KeesvdBerg/TDM-Test-Setup/Solidworks model of prototype/Motor mounting plate.SLDPRT

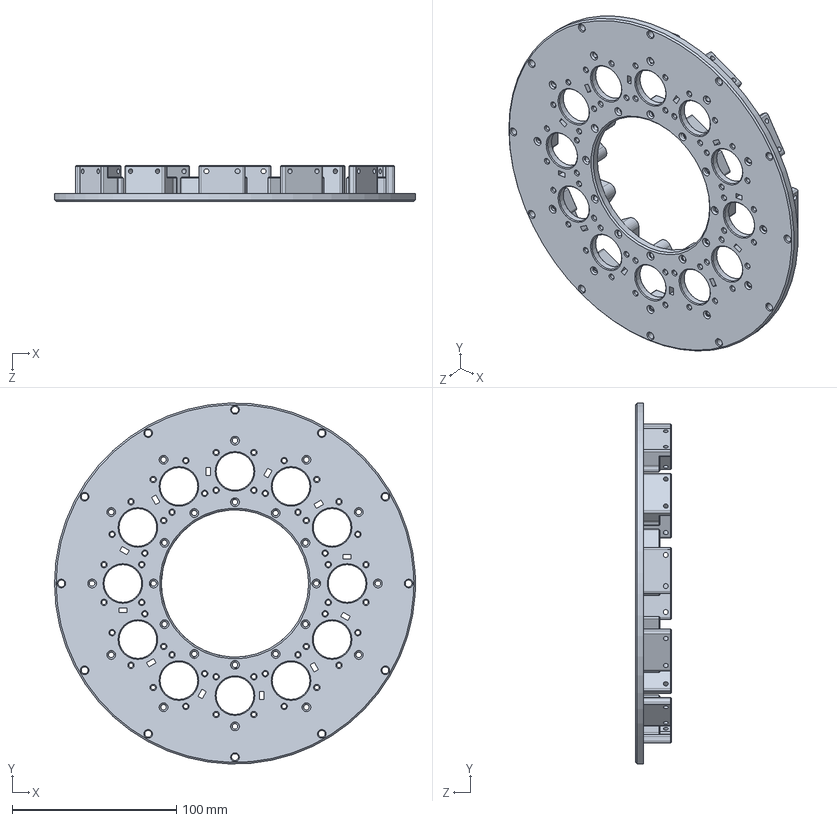
[picture p15: CAD file, 2024-05-05]
Solidworks model of prototype/Motor mounting plate.SLDPRT
220.0 x 219.9 x 22.0 mm
