KeesvdBerg/TDM-Test-Setup/Solidworks model of prototype/Magnet 5mm-5mm.SLDPRT

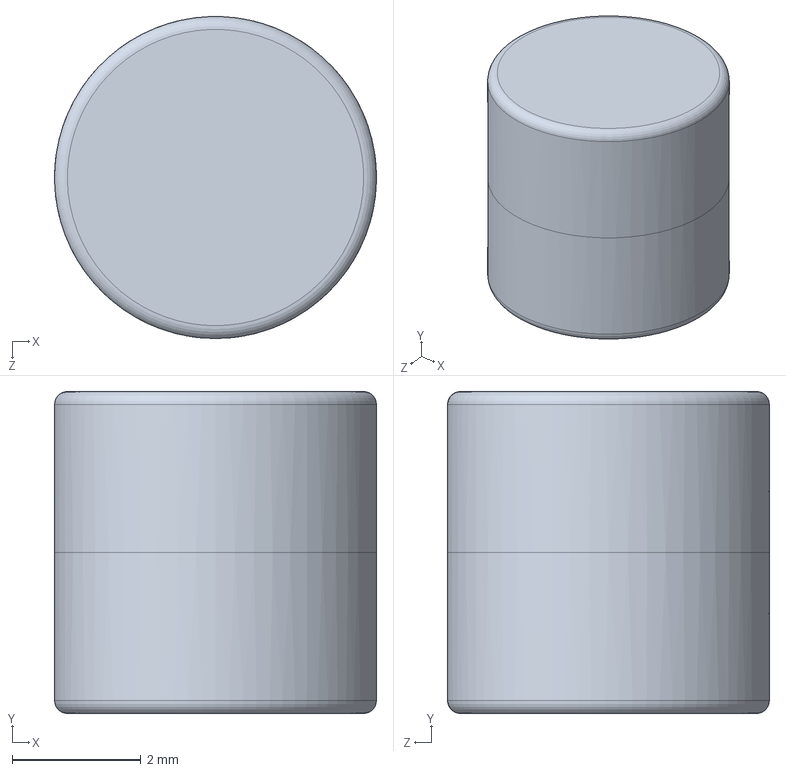
[picture p16: CAD file, 2024-05-05]
Solidworks model of prototype/Magnet 5mm-5mm.SLDPRT
5.00 x 5.00 x 5.00 mm
