KeesvdBerg/TDM-Test-Setup/Solidworks model of prototype/Heat set insert.SLDPRT

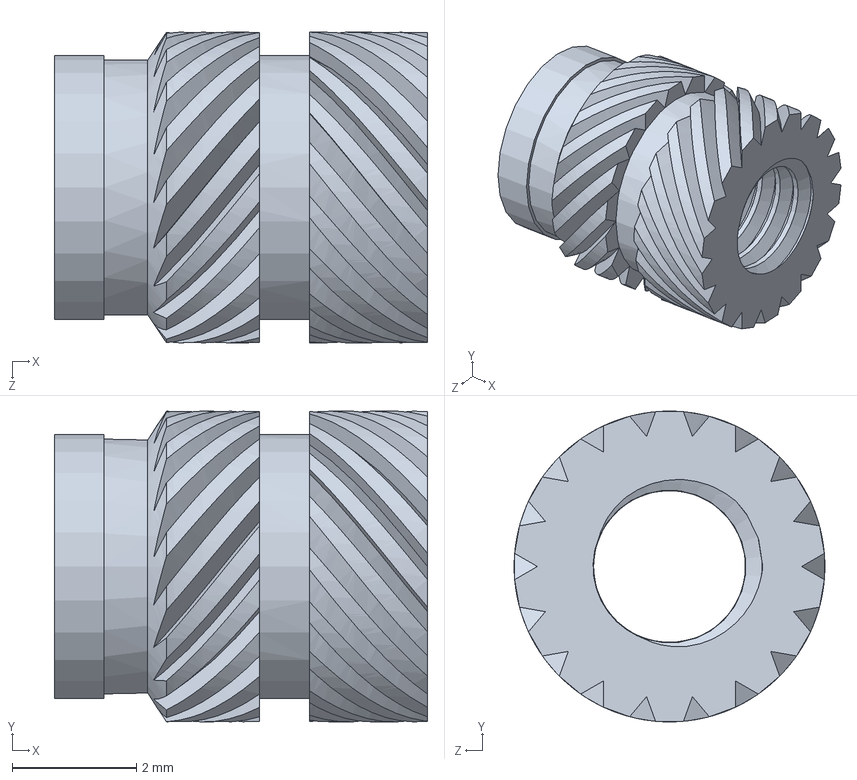
[picture p17: CAD file, 2024-05-05]
Solidworks model of prototype/Heat set insert.SLDPRT
6.00 x 5.00 x 5.00 mm
