KeesvdBerg/TDM-Test-Setup/Solidworks model of prototype/MTI lock mounting plate.SLDPRT

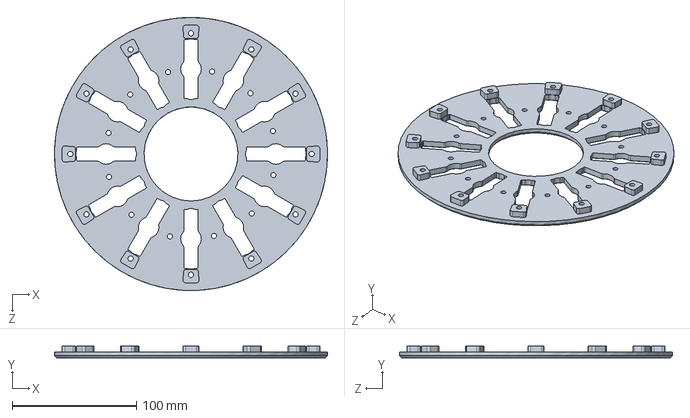
[picture p18: CAD file, 2024-05-05]
Solidworks model of prototype/MTI lock mounting plate.SLDPRT
219.9 x 10.0 x 220.0 mm
