KeesvdBerg/TDM-Test-Setup/Solidworks model of prototype/Acme thread.SLDPRT

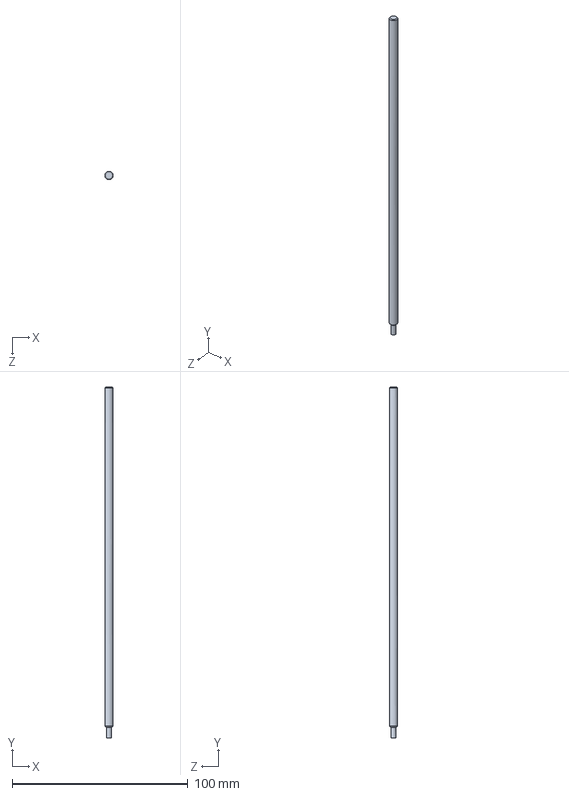
[picture p19: CAD file, 2024-05-05]
Solidworks model of prototype/Acme thread.SLDPRT
4.75 x 200.0 x 4.76 mm
