KeesvdBerg/TDM-Test-Setup/Solidworks model of prototype/Distal connector ring.SLDPRT

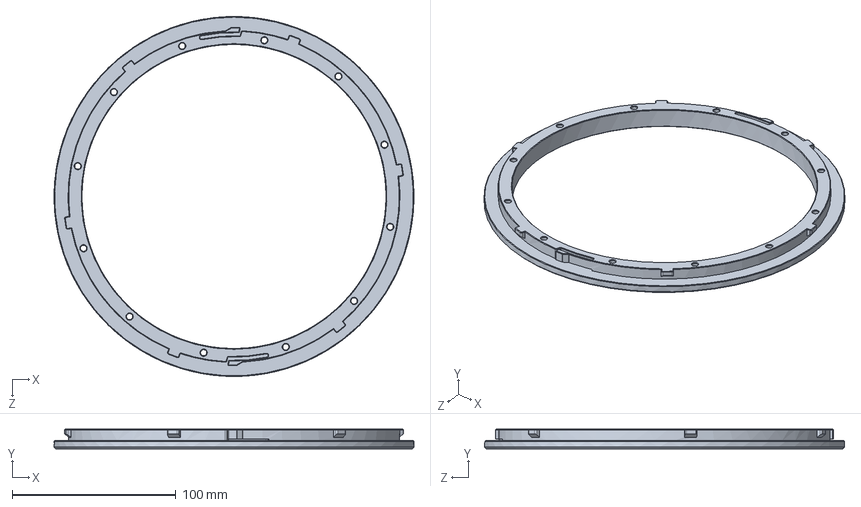
[picture p20: CAD file, 2024-05-05]
Solidworks model of prototype/Distal connector ring.SLDPRT
219.9 x 12.0 x 220.0 mm
