KeesvdBerg/TDM-Test-Setup/Solidworks model of prototype/Hall sensor DRV5505.SLDPRT

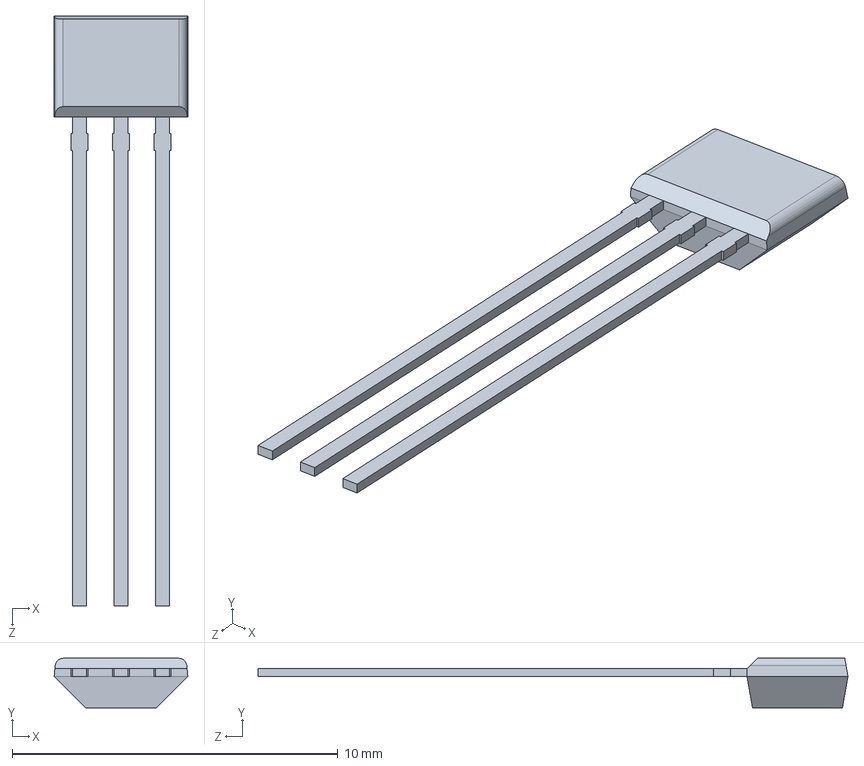
[picture p21: CAD file, 2024-05-05]
Solidworks model of prototype/Hall sensor DRV5505.SLDPRT
4.10 x 1.52 x 18.1 mm
