KeesvdBerg/TDM-Test-Setup/Solidworks model of prototype/Force sensor body.SLDPRT

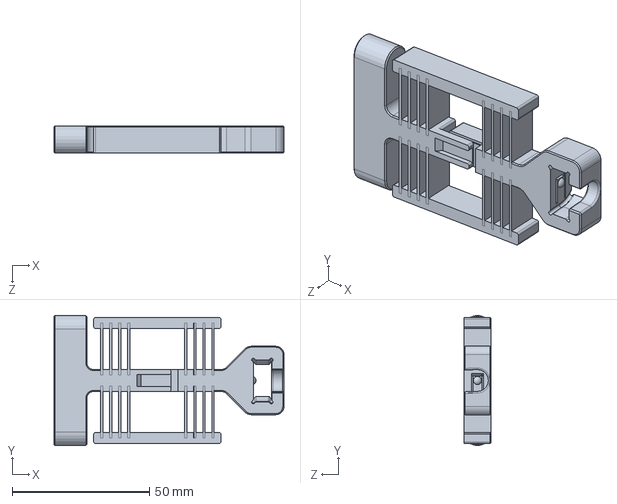
[picture p22: CAD file, 2024-05-05]
Solidworks model of prototype/Force sensor body.SLDPRT
83.9 x 47.5 x 10.0 mm
