KeesvdBerg/TDM-Test-Setup/Solidworks model of prototype/Limit switch board.SLDPRT

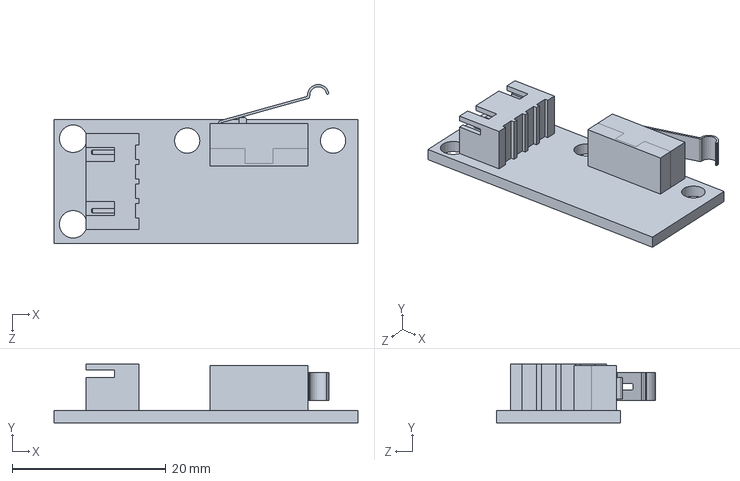
[picture p23: CAD file, 2024-05-05]
Solidworks model of prototype/Limit switch board.SLDPRT
39.6 x 7.63 x 20.7 mm
