KeesvdBerg/TDM-Test-Setup/Solidworks model of prototype/Tendon MTI.SLDPRT

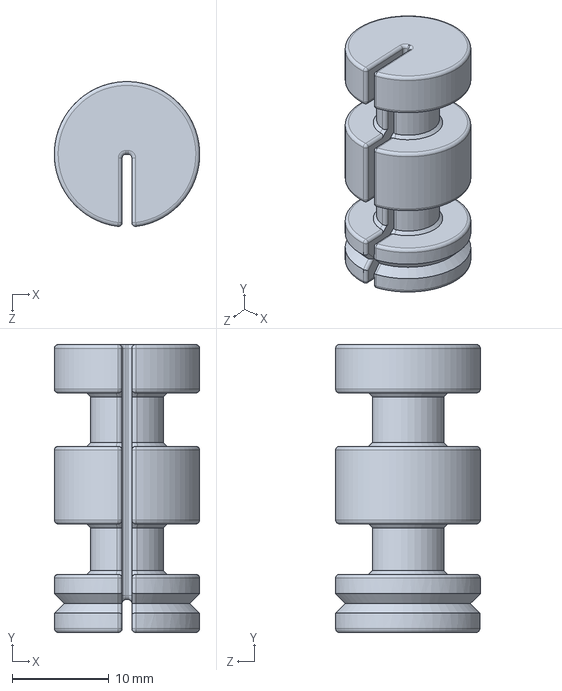
[picture p24: CAD file, 2024-05-05]
Solidworks model of prototype/Tendon MTI.SLDPRT
15.0 x 29.7 x 14.9 mm
