KeesvdBerg/TDM-Test-Setup/Solidworks model of prototype/Instrument adapter.SLDPRT

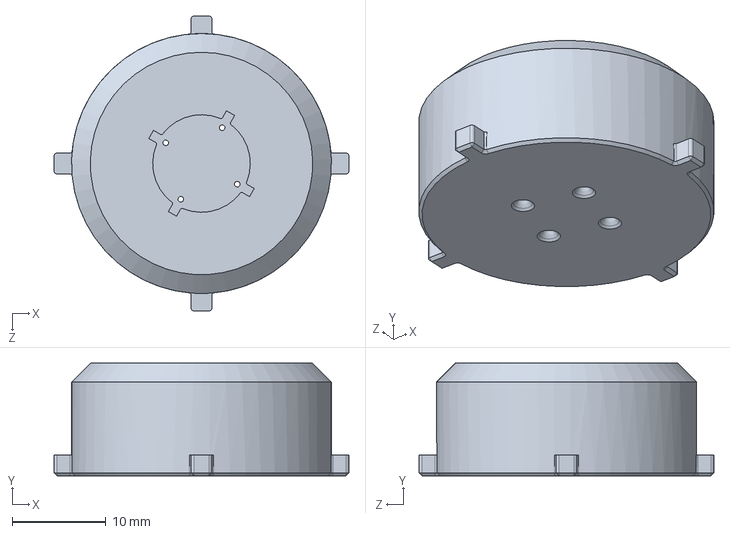
[picture p25: CAD file, 2024-05-05]
Solidworks model of prototype/Instrument adapter.SLDPRT
31.4 x 12.0 x 31.4 mm
