KeesvdBerg/TDM-Test-Setup/Solidworks model of prototype/MTI Lock spacer.SLDPRT

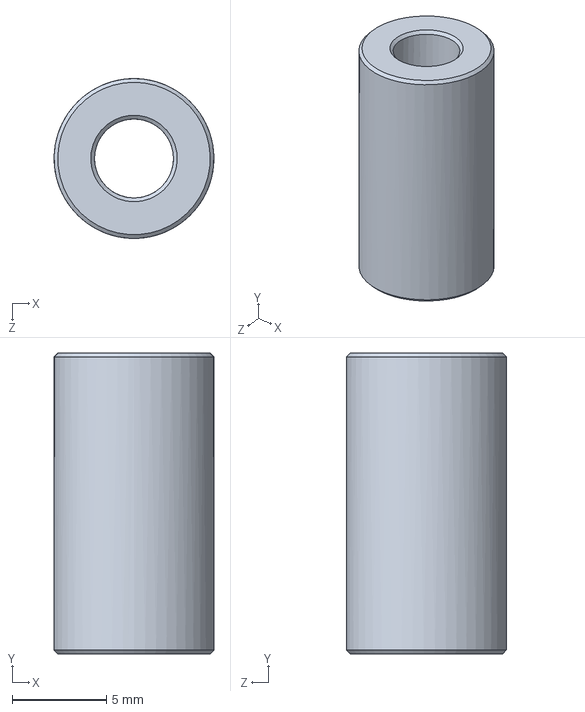
[picture p26: CAD file, 2024-05-05]
Solidworks model of prototype/MTI Lock spacer.SLDPRT
8.49 x 16.0 x 8.50 mm
