KeesvdBerg/TDM-Test-Setup/Solidworks model of prototype/M3 heat set insert.SLDPRT

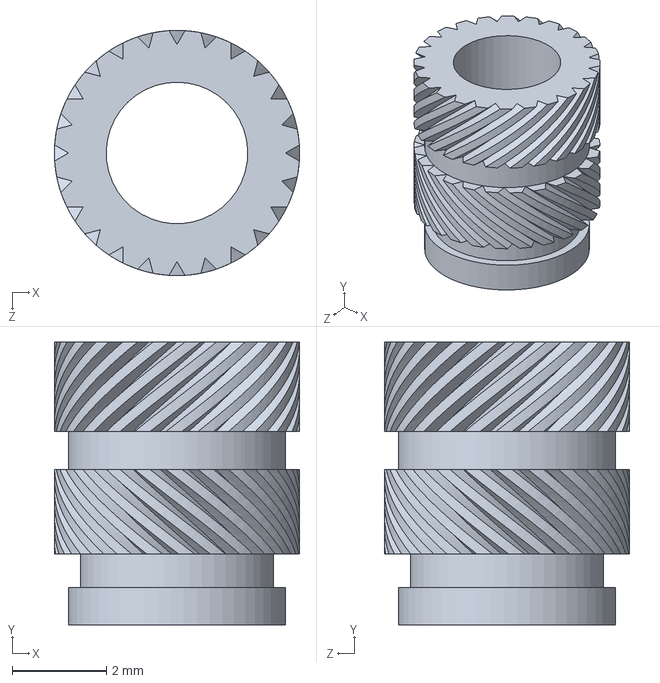
[picture p27: CAD file, 2024-05-05]
Solidworks model of prototype/M3 heat set insert.SLDPRT
5.20 x 6.00 x 5.20 mm
