KeesvdBerg/TDM-Test-Setup/Solidworks model of prototype/electronics housing inside setup.SLDPRT

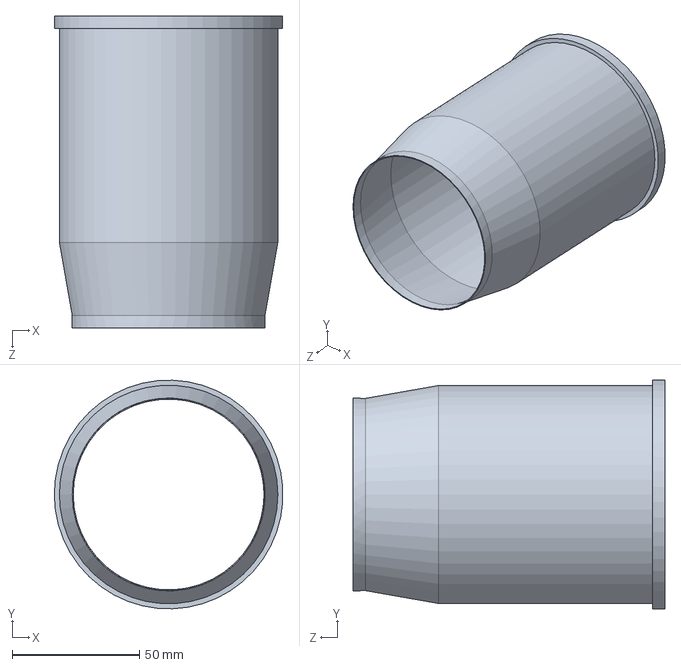
[picture p28: CAD file, 2024-05-05]
Solidworks model of prototype/electronics housing inside setup.SLDPRT
89.7 x 89.7 x 122.5 mm
