KeesvdBerg/TDM-Test-Setup/Solidworks model of prototype/M4 threaded rod 130 mm.SLDPRT

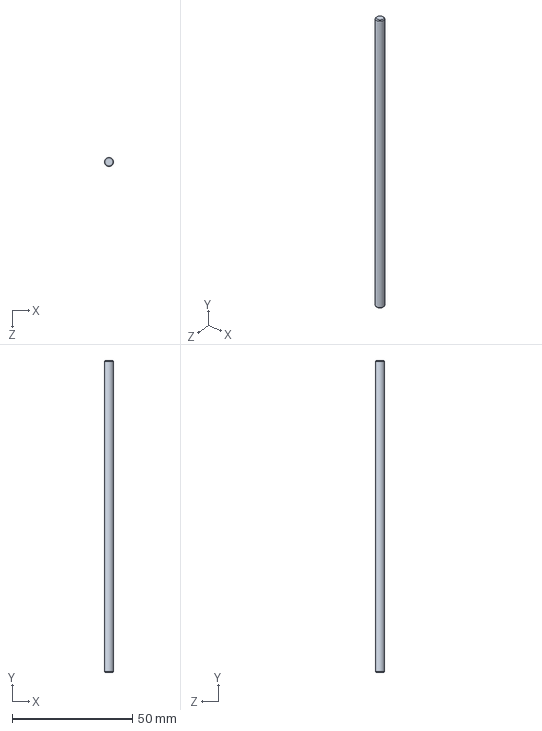
[picture p29: CAD file, 2024-05-05]
Solidworks model of prototype/M4 threaded rod 130 mm.SLDPRT
3.77 x 130.0 x 3.80 mm
