KeesvdBerg/TDM-Test-Setup/Solidworks model of prototype/Tendon diffuser.SLDPRT

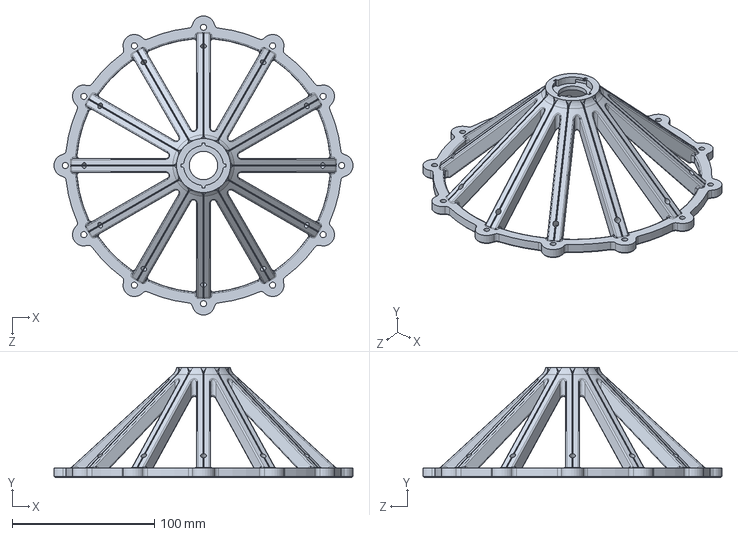
[picture p30: CAD file, 2024-05-05]
Solidworks model of prototype/Tendon diffuser.SLDPRT
210.4 x 77.7 x 210.4 mm
