KeesvdBerg/TDM-Test-Setup/Solidworks model of prototype/Nema 11 non-captive stepper motor.SLDPRT

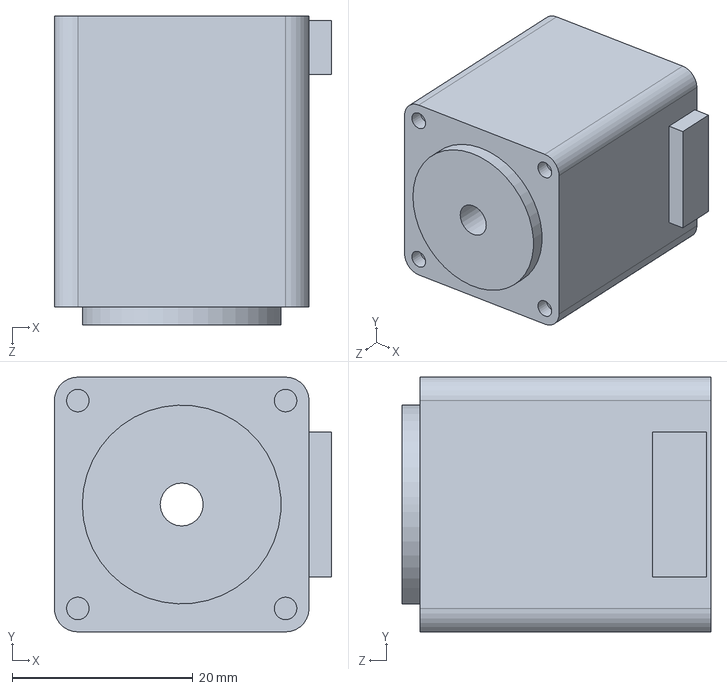
[picture p31: CAD file, 2024-05-05]
Solidworks model of prototype/Nema 11 non-captive stepper motor.SLDPRT
30.7 x 28.2 x 34.2 mm
