KeesvdBerg/TDM-Test-Setup/Solidworks model of prototype/Locking tab mounting plate test print.SLDPRT

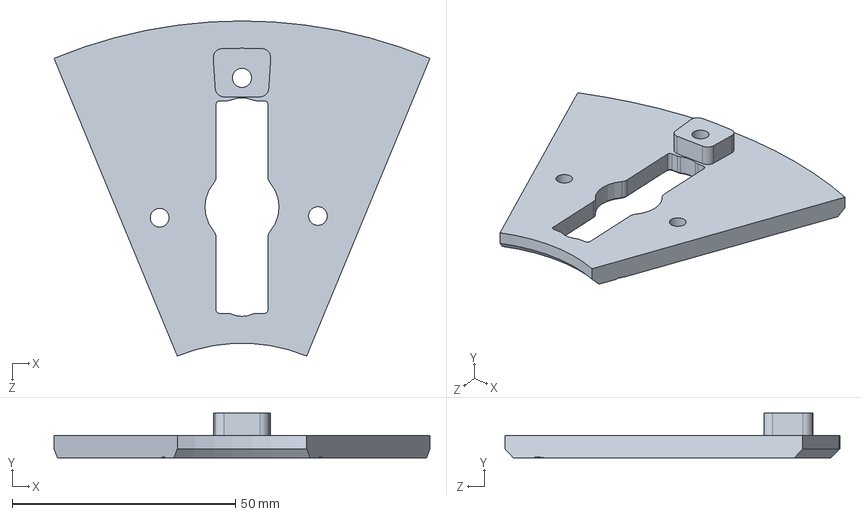
[picture p32: CAD file, 2024-05-05]
Solidworks model of prototype/Locking tab mounting plate test print.SLDPRT
84.2 x 10.0 x 75.0 mm
