KeesvdBerg/TDM-Test-Setup/Solidworks model of prototype/M4 eye hook.SLDPRT

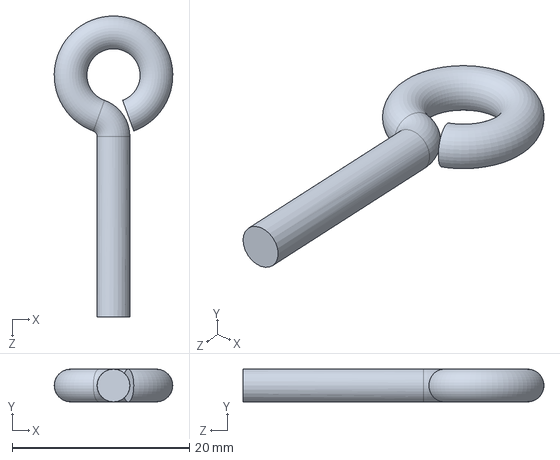
[picture p33: CAD file, 2024-05-05]
Solidworks model of prototype/M4 eye hook.SLDPRT
13.4 x 3.70 x 34.0 mm
