KeesvdBerg/TDM-Test-Setup/Solidworks model of prototype/Guiding rod 3 mm.SLDPRT

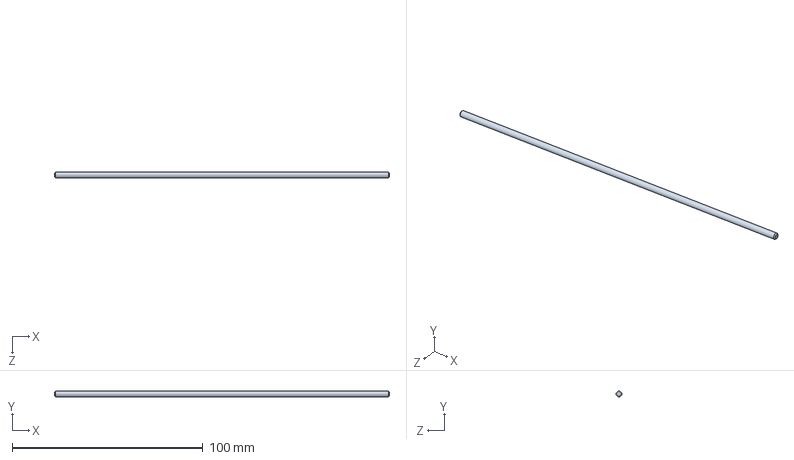
[picture p34: CAD file, 2024-05-05]
Solidworks model of prototype/Guiding rod 3 mm.SLDPRT
175.5 x 3.00 x 3.00 mm
